Everton-LF-Santos/Projeto-Integrador-3-2018-1/ajuste_ganho/adjusta.png

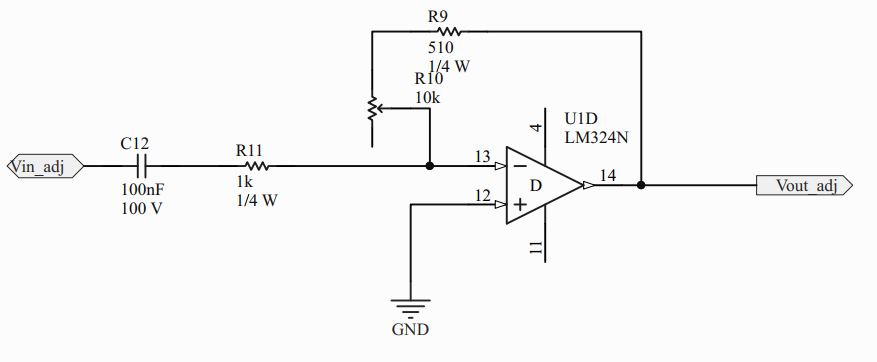
ajuste_ganho/adjusta.png
