Everton-LF-Santos/Projeto-Integrador-3-2018-1/ajuste_ganho/aop_adj.png

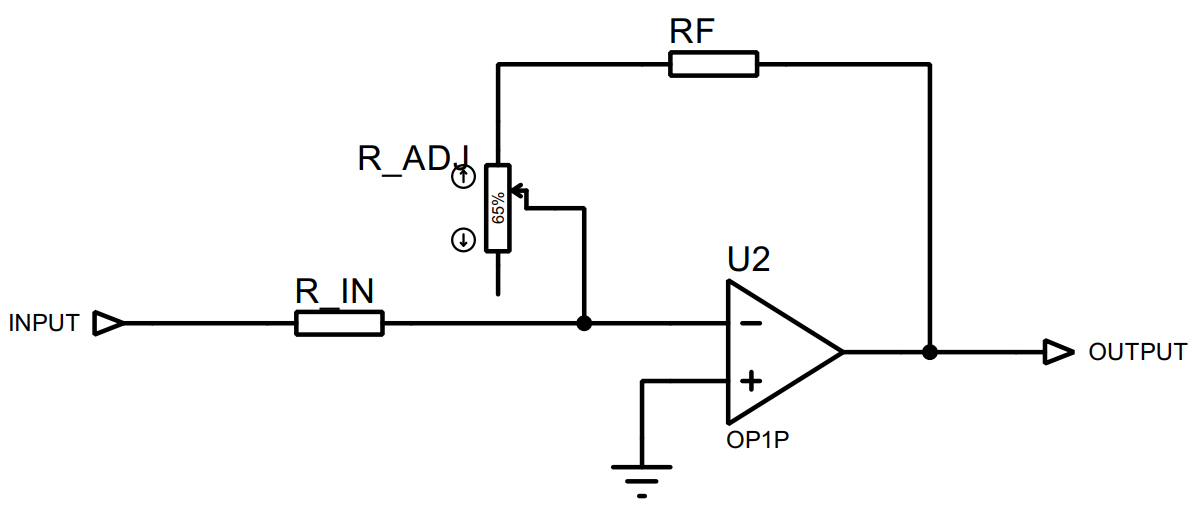
ajuste_ganho/aop_adj.png
