Everton-LF-Santos/Projeto-Integrador-3-2018-1/images/1_x_2.png

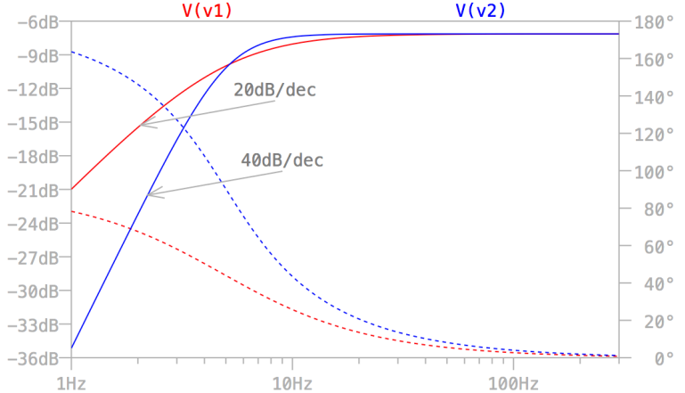
images/1_x_2.png
