Everton-LF-Santos/Projeto-Integrador-3-2018-1/images/9ee38d1a85d37fa23f86a14d3a9776ff67b0ec0f3b.gif

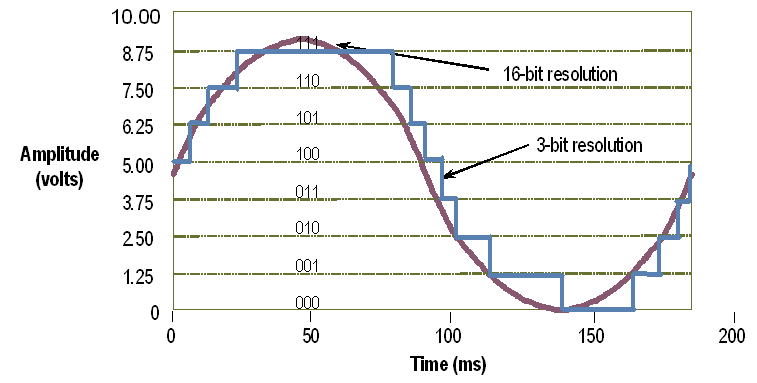
images/9ee38d1a85d37fa23f86a14d3a9776ff67b0ec0f3b.gif
