Everton-LF-Santos/Projeto-Integrador-3-2018-1/images/AOP_INSTR.png

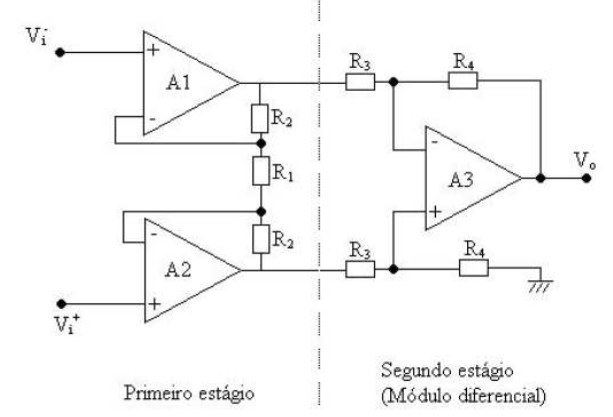
images/AOP_INSTR.png
