Everton-LF-Santos/Projeto-Integrador-3-2018-1/images/block_diagram.jpg

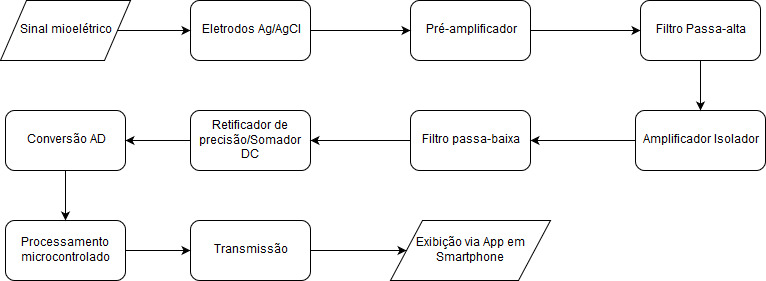
images/block_diagram.jpg
