Everton-LF-Santos/Projeto-Integrador-3-2018-1/images/Capturar1.PNG

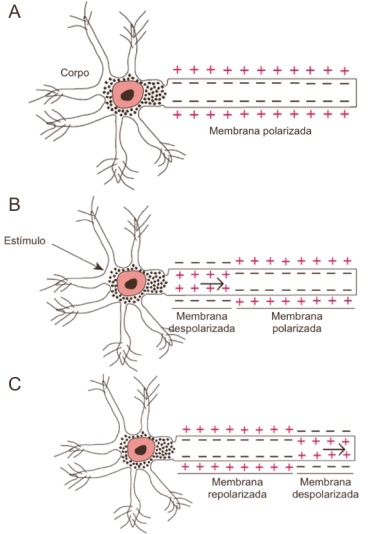
images/Capturar1.PNG
