Everton-LF-Santos/Projeto-Integrador-3-2018-1/images/Capturar2.PNG

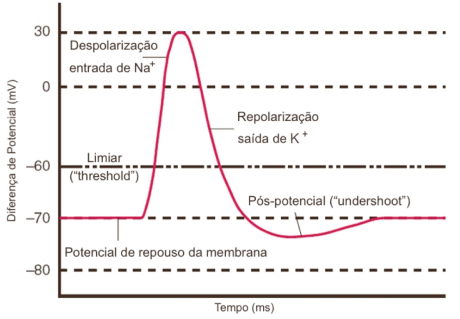
images/Capturar2.PNG
