Everton-LF-Santos/Projeto-Integrador-3-2018-1/images/Capturar3.PNG

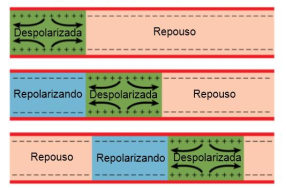
images/Capturar3.PNG
