Everton-LF-Santos/Projeto-Integrador-3-2018-1/images/Capturar4.PNG

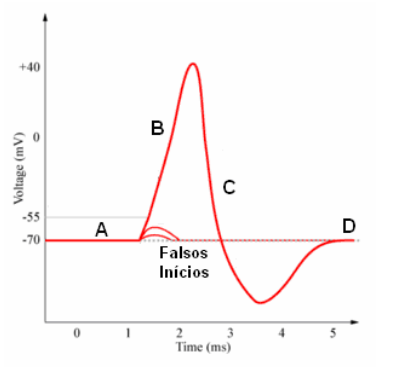
images/Capturar4.PNG
