Everton-LF-Santos/Projeto-Integrador-3-2018-1/images/Capturar5.PNG

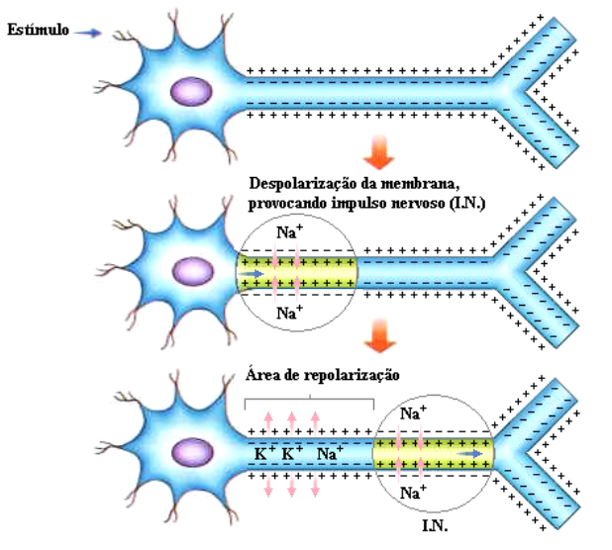
images/Capturar5.PNG
