Everton-LF-Santos/Projeto-Integrador-3-2018-1/images/eletrodo-descartavel-espuma-ref-2223-brq-c-50-3m.jpg

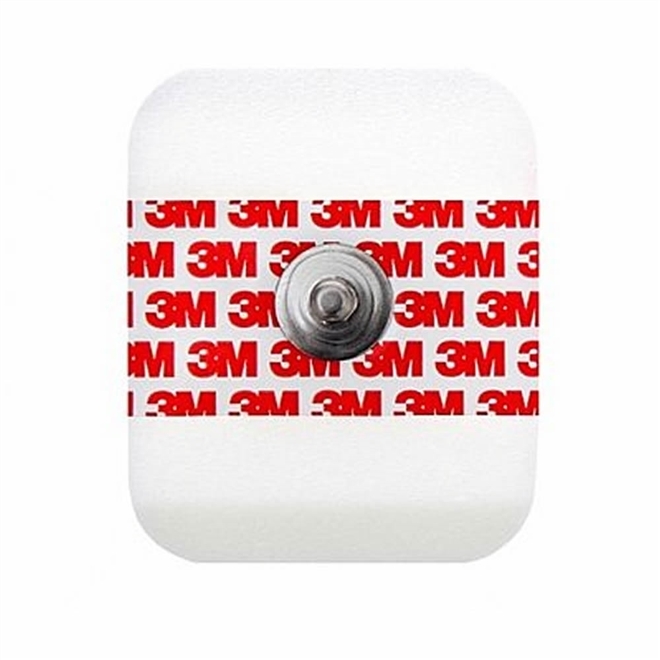
images/eletrodo-descartavel-espuma-ref-2223-brq-c-50-3m.jpg
