Everton-LF-Santos/Projeto-Integrador-3-2018-1/images/eletrodos.png

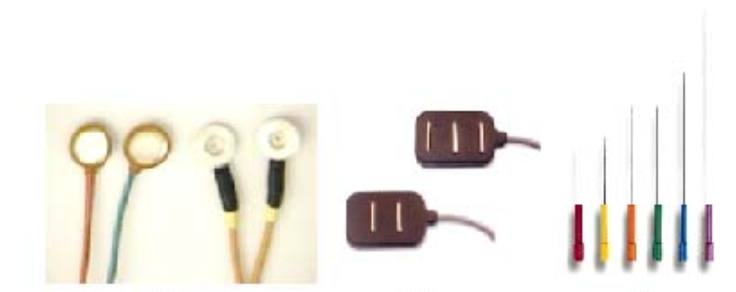
images/eletrodos.png
