Everton-LF-Santos/Projeto-Integrador-3-2018-1/images/eletrods.png

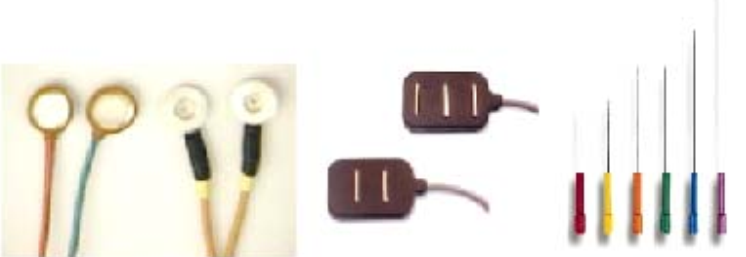
images/eletrods.png
