Everton-LF-Santos/Projeto-Integrador-3-2018-1/images/espectro_de_potencia.png

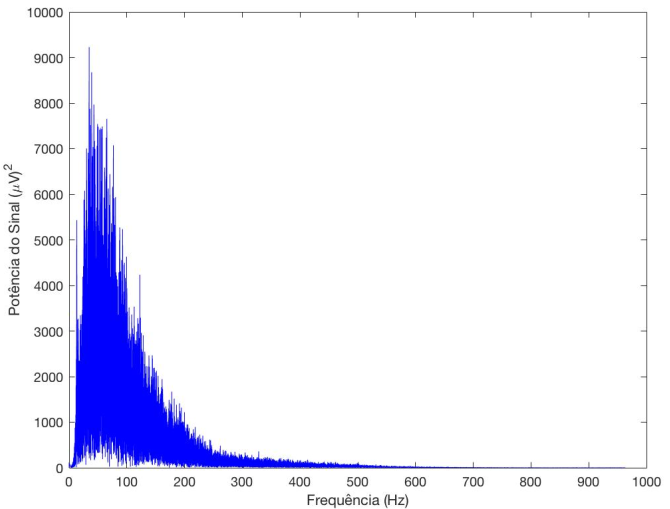
images/espectro_de_potencia.png
