Everton-LF-Santos/Projeto-Integrador-3-2018-1/images/fcorte.png

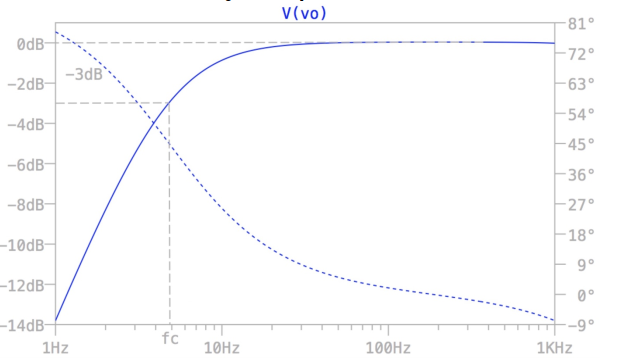
images/fcorte.png
