Everton-LF-Santos/Projeto-Integrador-3-2018-1/images/filtrox.png

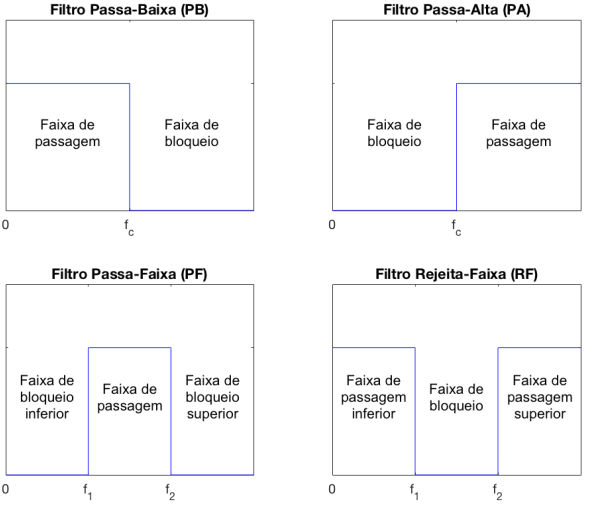
images/filtrox.png
