Everton-LF-Santos/Projeto-Integrador-3-2018-1/images/ganho_quasi.png

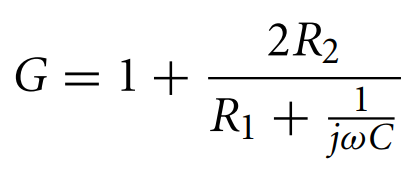
images/ganho_quasi.png
