Everton-LF-Santos/Projeto-Integrador-3-2018-1/images/ina118.png

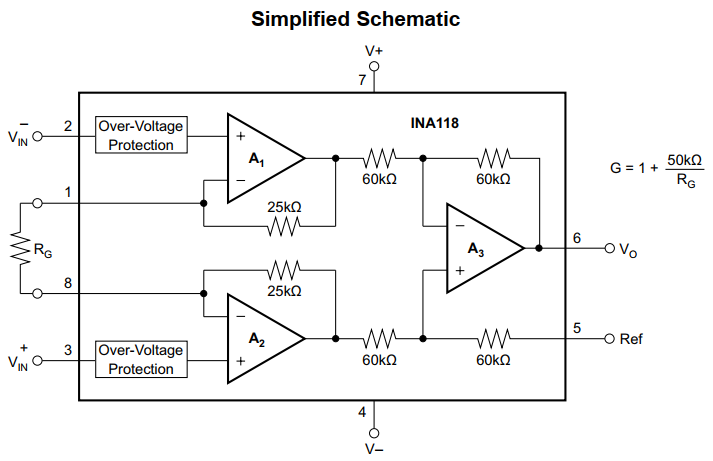
images/ina118.png
