Everton-LF-Santos/Projeto-Integrador-3-2018-1/images/instru_ina118.png

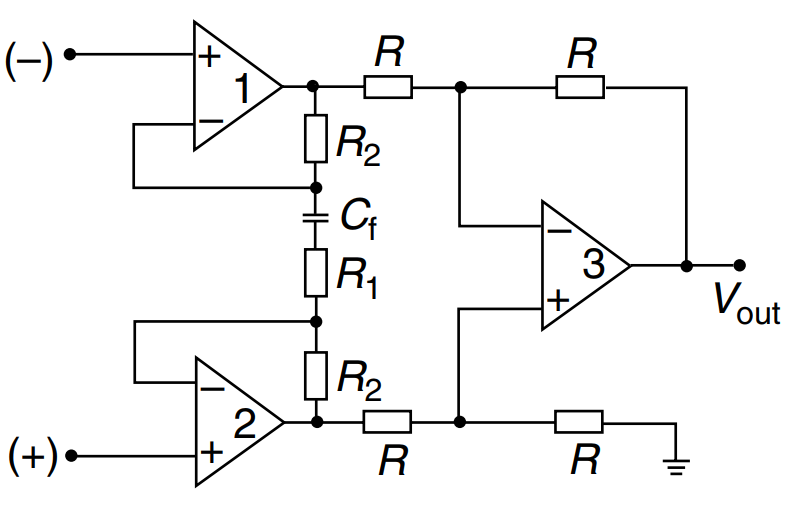
images/instru_ina118.png
