Everton-LF-Santos/Projeto-Integrador-3-2018-1/images/muapt_e_emg.PNG

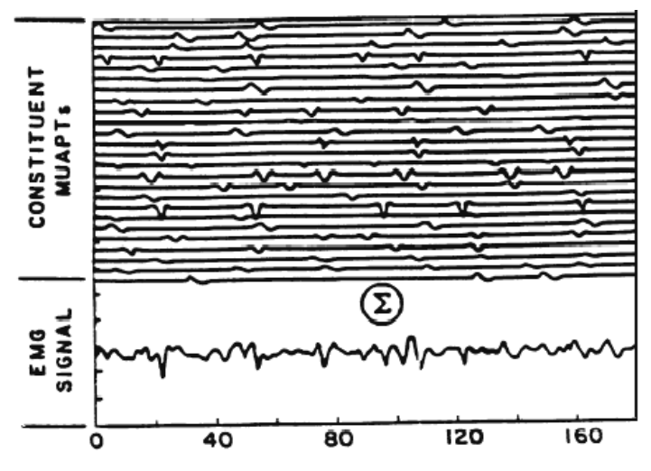
images/muapt_e_emg.PNG
