Everton-LF-Santos/Projeto-Integrador-3-2018-1/images/regiao_musculo.png

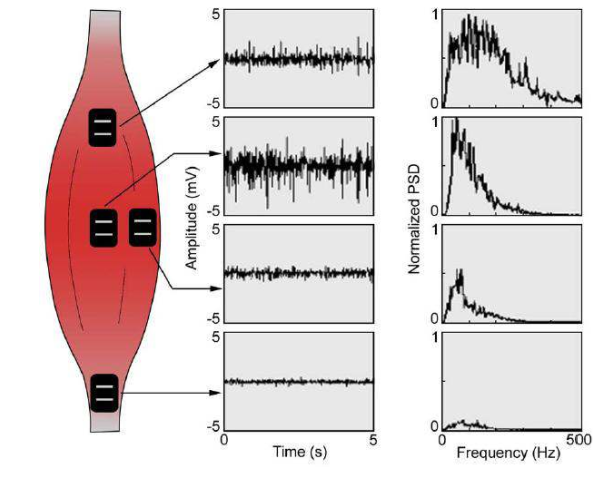
images/regiao_musculo.png
