Everton-LF-Santos/Projeto-Integrador-3-2018-1/passa_baixa/filtro_pb_calculo.png

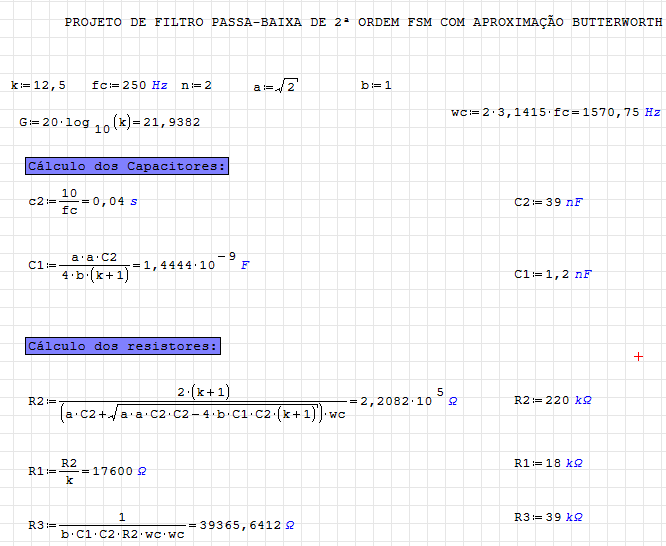
passa_baixa/filtro_pb_calculo.png
