Everton-LF-Santos/Projeto-Integrador-3-2018-1/passa_baixa/PB2_MFB_BUTTERWORTH V2.JPG

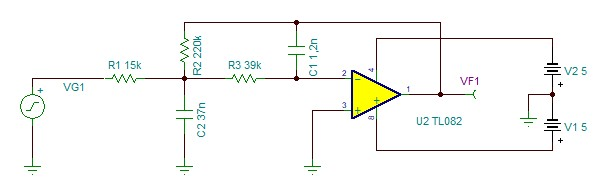
passa_baixa/PB2_MFB_BUTTERWORTH V2.JPG
