Everton-LF-Santos/Projeto-Integrador-3-2018-1/passa_baixa/simula_filtro_pb.png

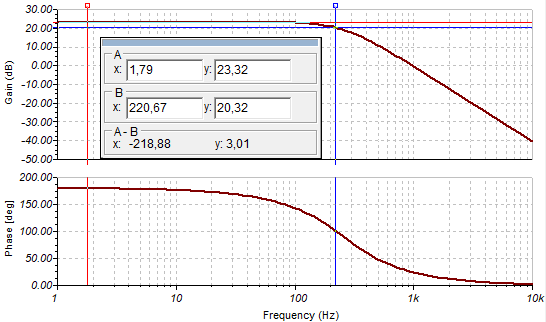
passa_baixa/simula_filtro_pb.png
