Everton-LF-Santos/Projeto-Integrador-3-2018-1/passa_baixa/topologia_mfb.png

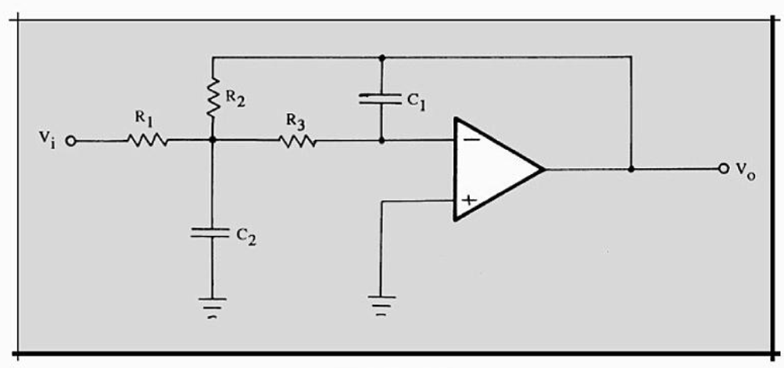
passa_baixa/topologia_mfb.png
