Everton-LF-Santos/Projeto-Integrador-3-2018-1/pre_amp_e_passa_alta/fpa + pre amp.JPG

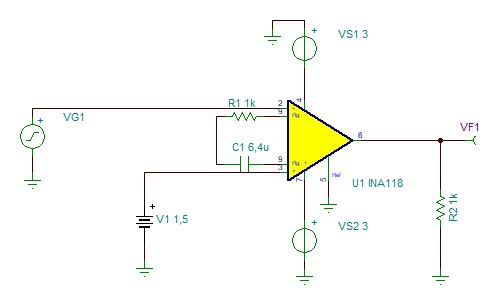
pre_amp_e_passa_alta/fpa + pre amp.JPG
