Everton-LF-Santos/Projeto-Integrador-3-2018-1/pre_amp_e_passa_alta/simula_filtro_pa.png

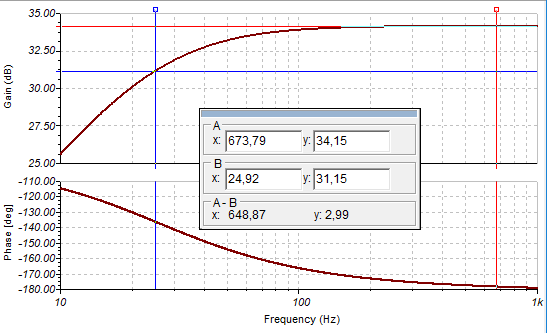
pre_amp_e_passa_alta/simula_filtro_pa.png
