Everton-LF-Santos/Projeto-Integrador-3-2018-1/somadorDC/offset_dc.png

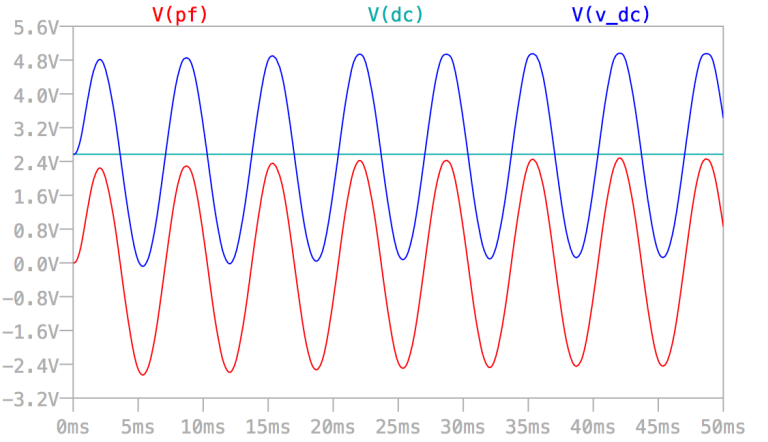
somadorDC/offset_dc.png
