Everton-LF-Santos/Projeto-Integrador-3-2018-1/somadorDC/somadc.png

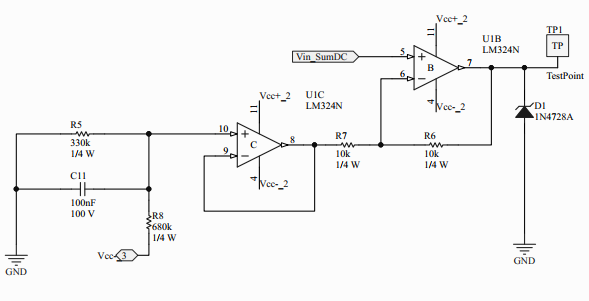
somadorDC/somadc.png
