Everton-LF-Santos/Projeto-Integrador-3-2018-1/somadorDC/somador_dc.png

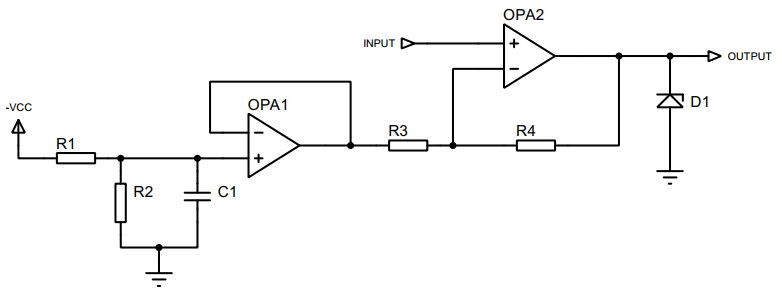
somadorDC/somador_dc.png
