Everton-LF-Santos/Projeto-Integrador-3-2018-1/prototipo_e_testes/filtro_pb/TEK0009.BMP

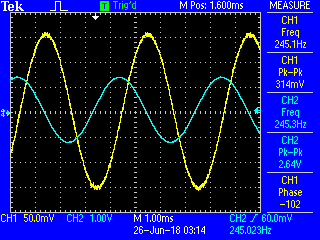
prototipo_e_testes/filtro_pb/TEK0009.BMP
