Everton-LF-Santos/Projeto-Integrador-3-2018-1/prototipo_e_testes/IMG_20180618_105822875.jpg

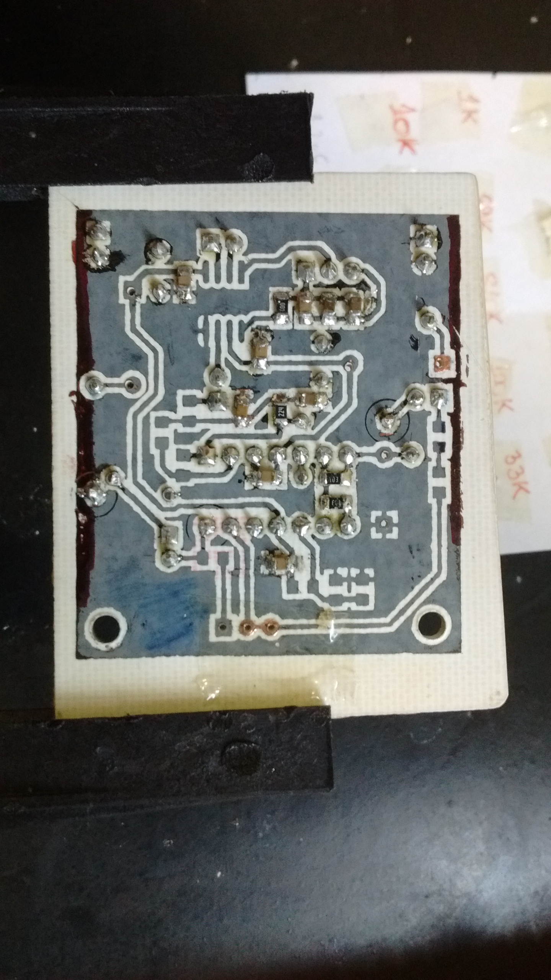
prototipo_e_testes/IMG_20180618_105822875.jpg
