Everton-LF-Santos/Projeto-Integrador-3-2018-1/prototipo_e_testes/pre_amp_pa/TEK0009.BMP

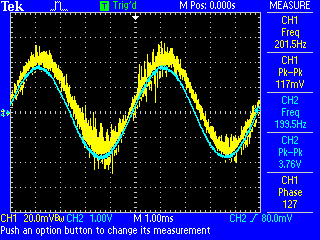
prototipo_e_testes/pre_amp_pa/TEK0009.BMP
